ArcadeTV/HuEverReset/HuEverReset_install_led.jpg

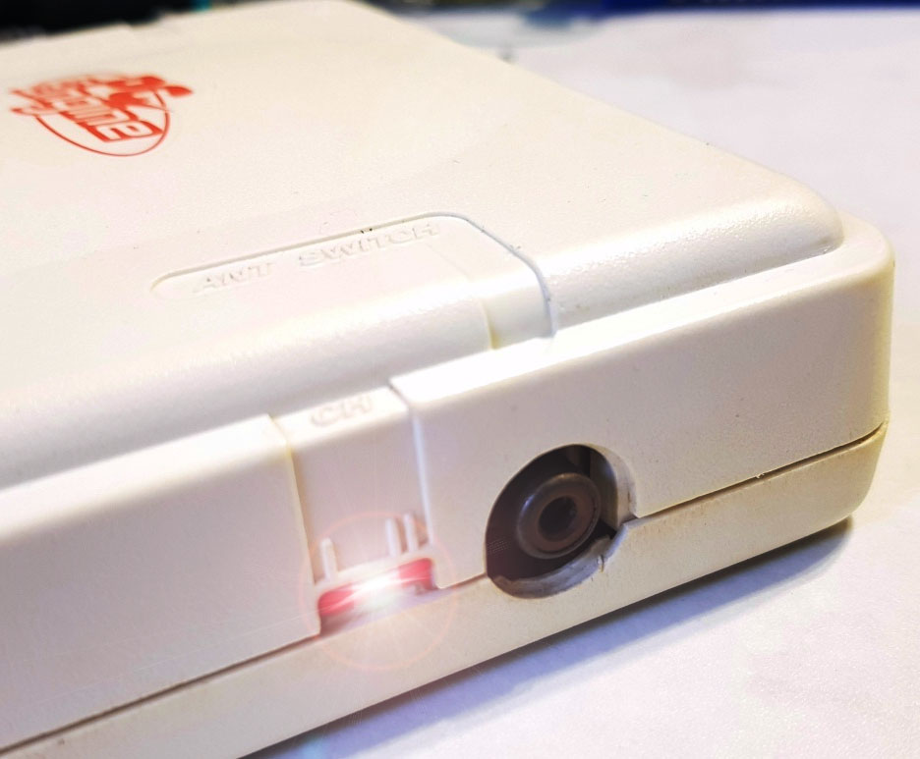
HuEverReset_install_led.jpg
